Matthew-Garcia/SCARA-Robot/3D_Models/Ball Bearing 35x47x7mm.SLDPRT

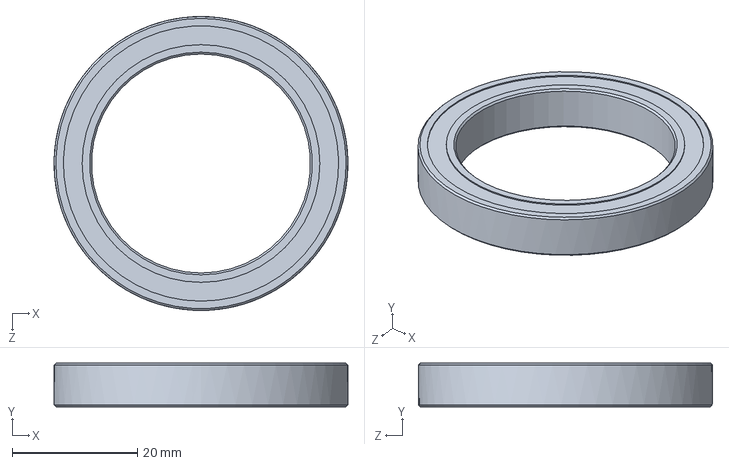
[picture p16: CAD file, 2025-07-01]
3D_Models/Ball Bearing 35x47x7mm.SLDPRT
47.0 x 7.00 x 47.0 mm
