Matthew-Garcia/SCARA-Robot/3D_Models/Arm 2 Cover.SLDPRT

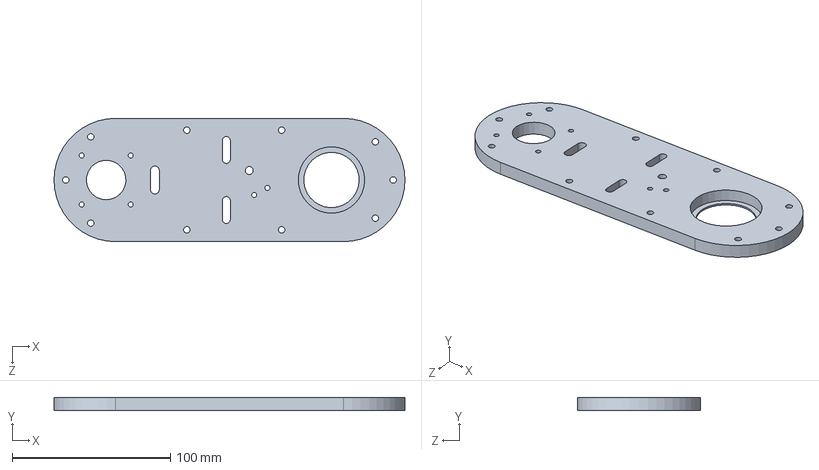
[picture p17: CAD file, 2025-07-01]
3D_Models/Arm 2 Cover.SLDPRT
222.0 x 8.00 x 78.0 mm
