Matthew-Garcia/SCARA-Robot/3D_Models/Z-axis Top Plate.SLDPRT

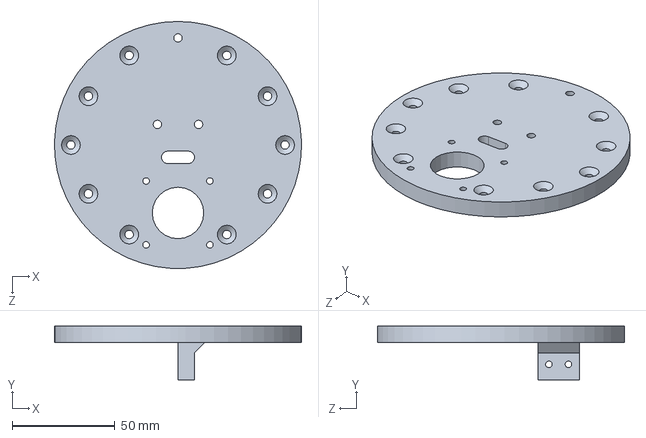
[picture p18: CAD file, 2025-07-01]
3D_Models/Z-axis Top Plate.SLDPRT
119.9 x 26.0 x 120.0 mm
