Matthew-Garcia/SCARA-Robot/3D_Models/Thrust Bearing - 40x60x13.SLDPRT

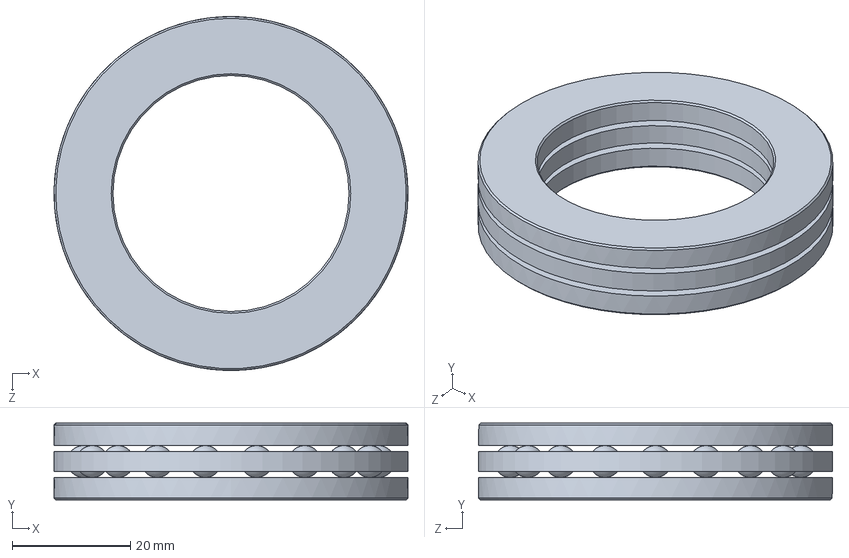
[picture p19: CAD file, 2025-07-01]
3D_Models/Thrust Bearing - 40x60x13.SLDPRT
60.0 x 13.0 x 60.0 mm
