Matthew-Garcia/SCARA-Robot/3D_Models/J3 Coupler.SLDPRT

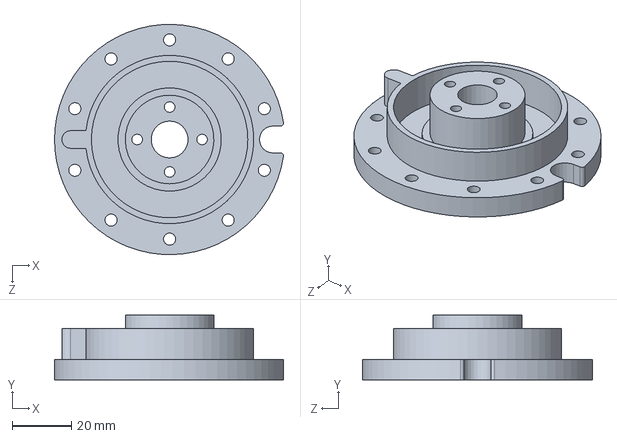
[picture p20: CAD file, 2025-07-01]
3D_Models/J3 Coupler.SLDPRT
77.6 x 22.0 x 78.0 mm
