Matthew-Garcia/SCARA-Robot/3D_Models/GT2 Belt 300mm 2.SLDPRT

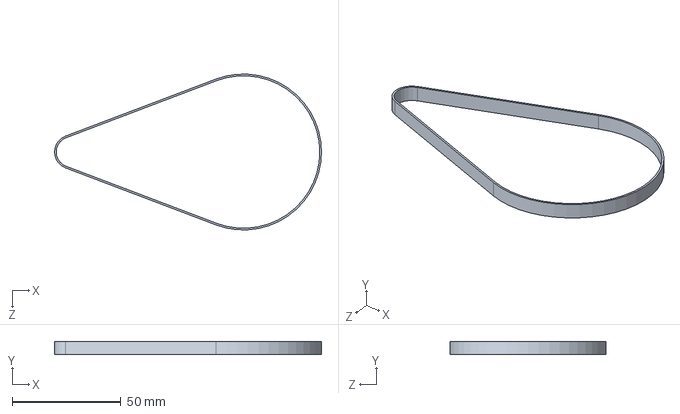
[picture p21: CAD file, 2025-07-01]
3D_Models/GT2 Belt 300mm 2.SLDPRT
122.6 x 6.00 x 71.5 mm
