Matthew-Garcia/SCARA-Robot/3D_Models/GT2 Belt 400mm.SLDPRT

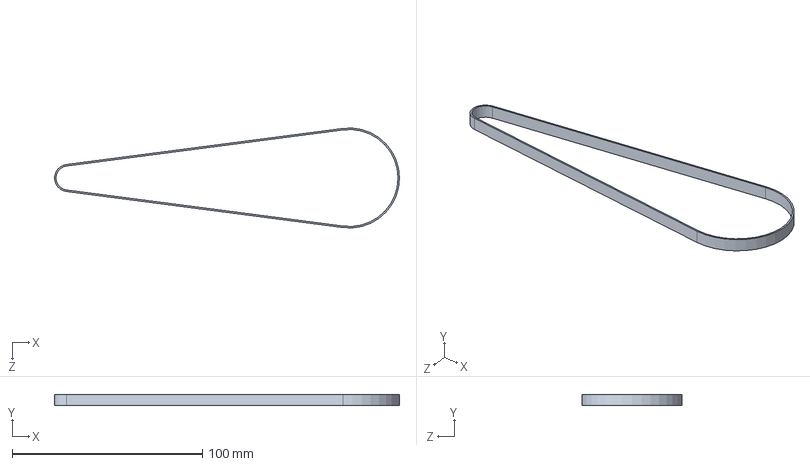
[picture p22: CAD file, 2025-07-01]
3D_Models/GT2 Belt 400mm.SLDPRT
181.4 x 6.00 x 52.5 mm
