Matthew-Garcia/SCARA-Robot/3D_Models/J1 coupler.SLDPRT

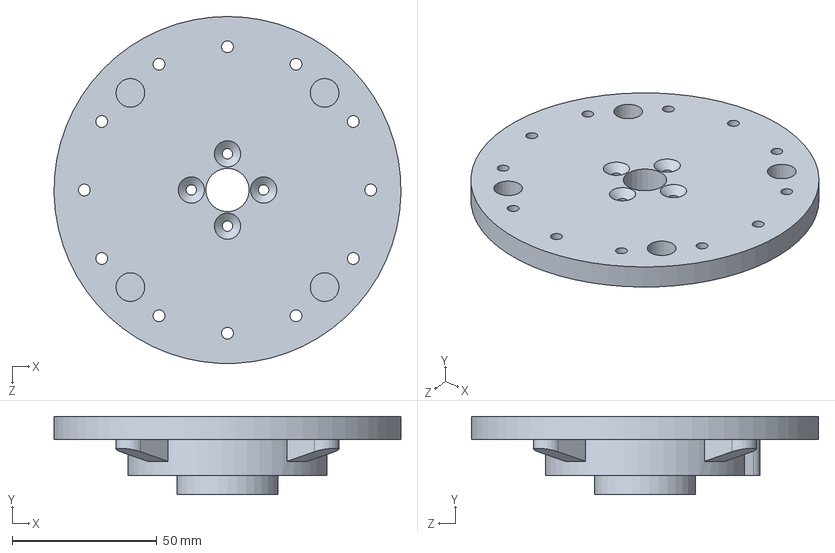
[picture p23: CAD file, 2025-07-01]
3D_Models/J1 coupler.SLDPRT
120.0 x 27.0 x 120.0 mm
