Matthew-Garcia/SCARA-Robot/3D_Models/Arm 2.SLDPRT

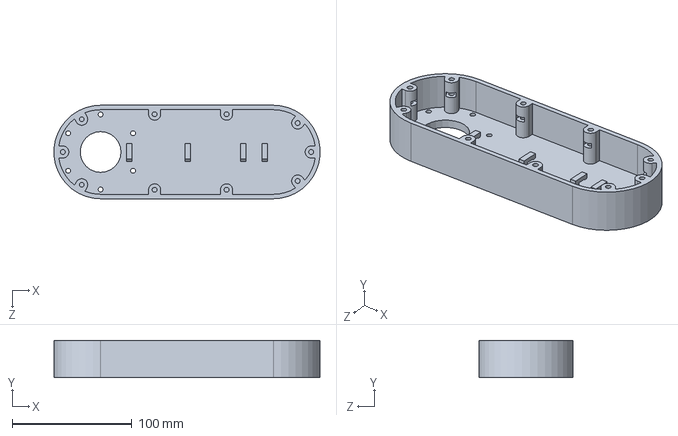
[picture p24: CAD file, 2025-07-01]
3D_Models/Arm 2.SLDPRT
221.7 x 31.0 x 78.0 mm
