Matthew-Garcia/SCARA-Robot/3D_Models/Gripper Mechanism Slider.SLDPRT

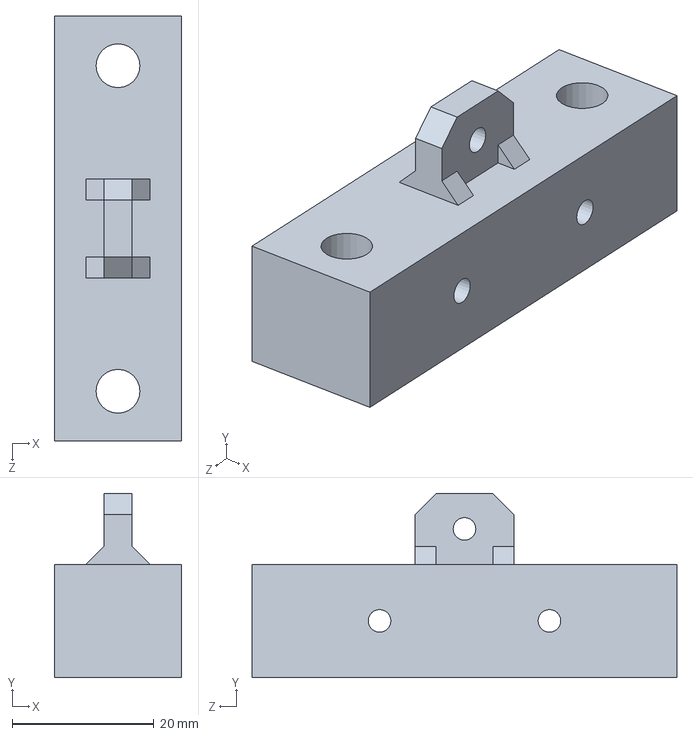
[picture p25: CAD file, 2025-07-01]
3D_Models/Gripper Mechanism Slider.SLDPRT
18.0 x 26.0 x 60.0 mm
