Matthew-Garcia/SCARA-Robot/3D_Models/Arduino UNO case p1.SLDPRT

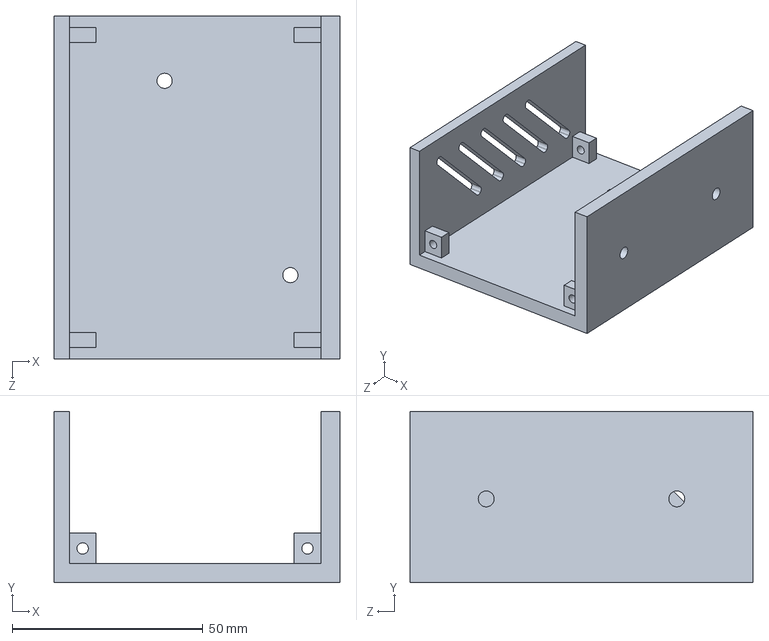
[picture p26: CAD file, 2025-07-01]
3D_Models/Arduino UNO case p1.SLDPRT
75.0 x 45.0 x 90.0 mm
