Matthew-Garcia/SCARA-Robot/3D_Models/Gripper End.SLDPRT

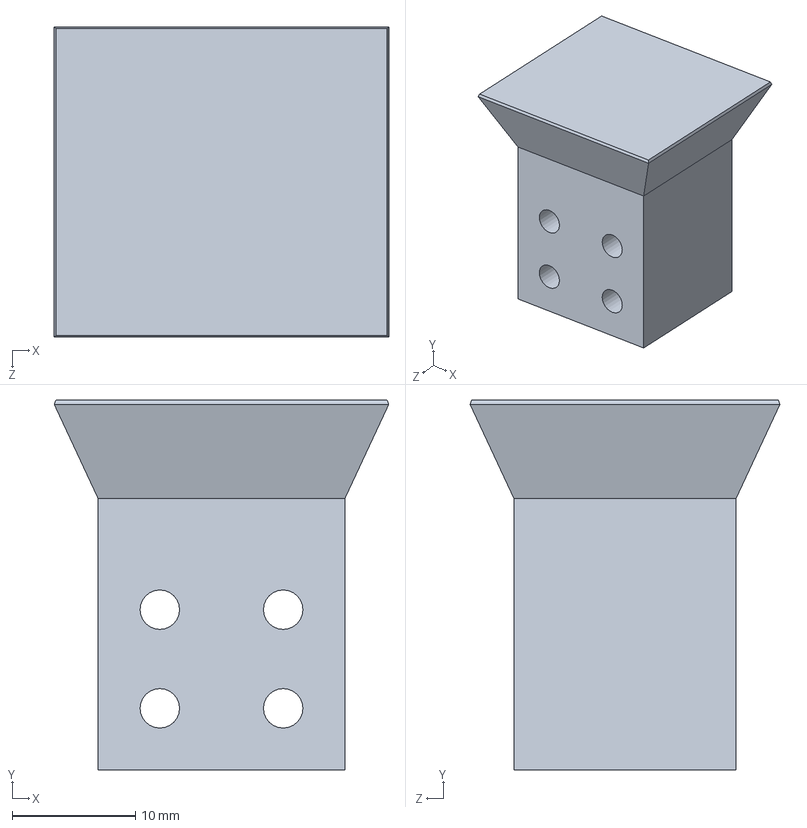
[picture p27: CAD file, 2025-07-01]
3D_Models/Gripper End.SLDPRT
27.1 x 30.0 x 25.1 mm
