Matthew-Garcia/SCARA-Robot/3D_Models/GT2 Pulley - 90 teeth - J3.SLDPRT

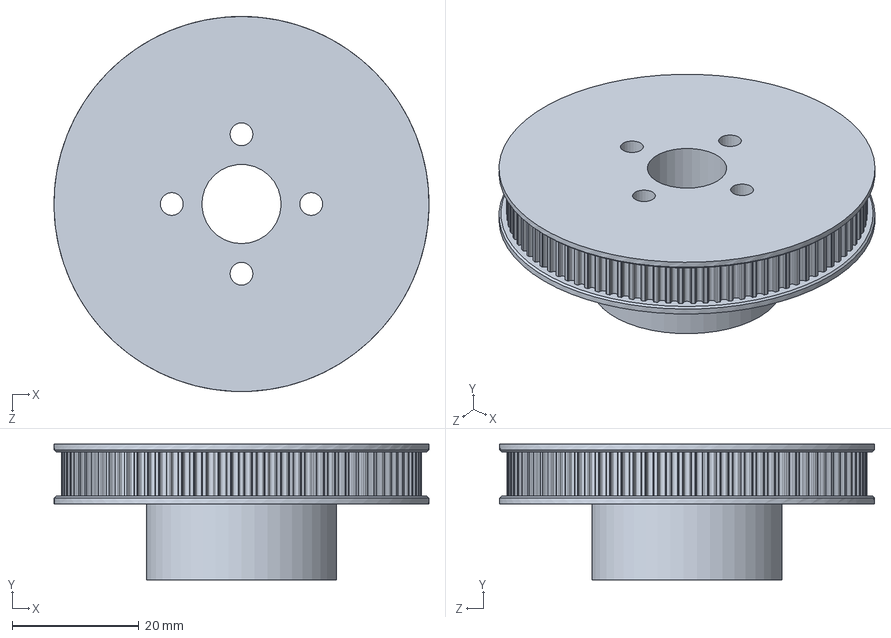
[picture p28: CAD file, 2025-07-01]
3D_Models/GT2 Pulley - 90 teeth - J3.SLDPRT
59.2 x 21.4 x 59.2 mm
