Matthew-Garcia/SCARA-Robot/3D_Models/Top cover.SLDPRT

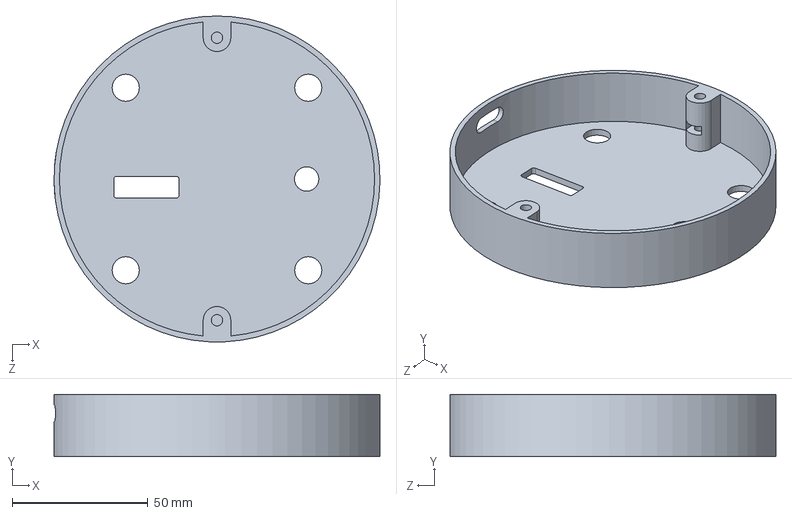
[picture p29: CAD file, 2025-07-01]
3D_Models/Top cover.SLDPRT
120.0 x 23.0 x 120.0 mm
