Matthew-Garcia/SCARA-Robot/3D_Models/Servo MG996R Horn.step

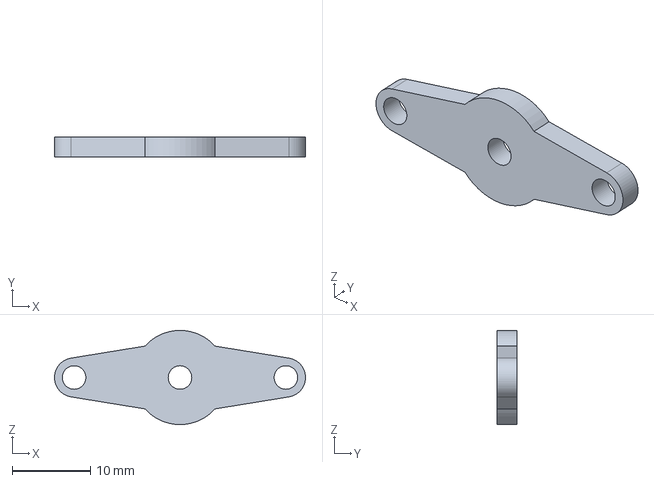
[picture p30: CAD file, 2025-07-01]
3D_Models/Servo MG996R Horn.step
32.0 x 2.50 x 12.0 mm
