Matthew-Garcia/SCARA-Robot/3D_Models/Base cover.SLDPRT

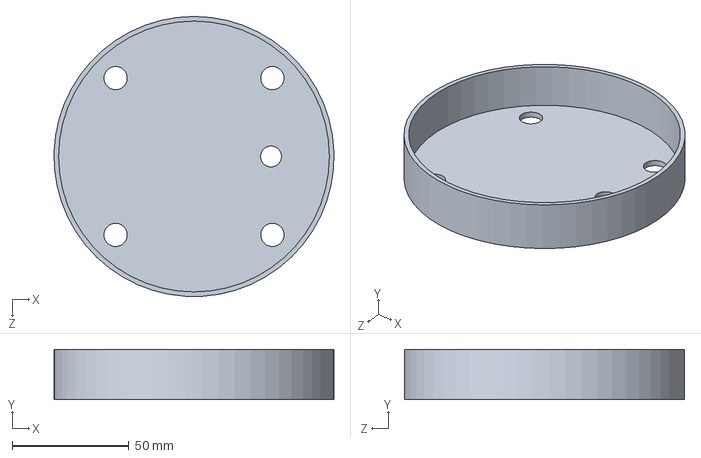
[picture p31: CAD file, 2025-07-01]
3D_Models/Base cover.SLDPRT
119.9 x 21.5 x 120.0 mm
