Matthew-Garcia/SCARA-Robot/3D_Models/Servo Motor MG996R 3D Model.step

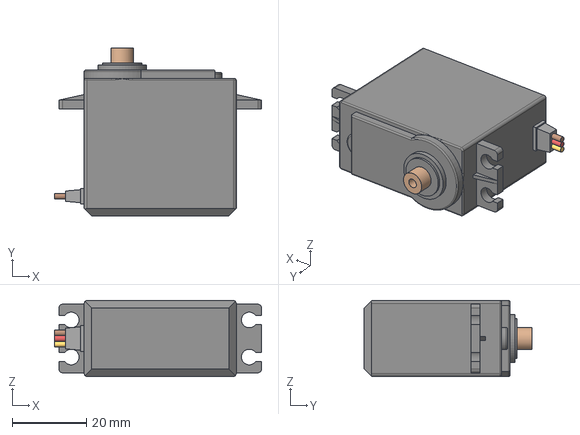
[picture p32: CAD file, 2025-07-01]
3D_Models/Servo Motor MG996R 3D Model.step
55.8 x 45.2 x 20.5 mm
