Matthew-Garcia/SCARA-Robot/3D_Models/Z-axis Bottom Plate.SLDPRT

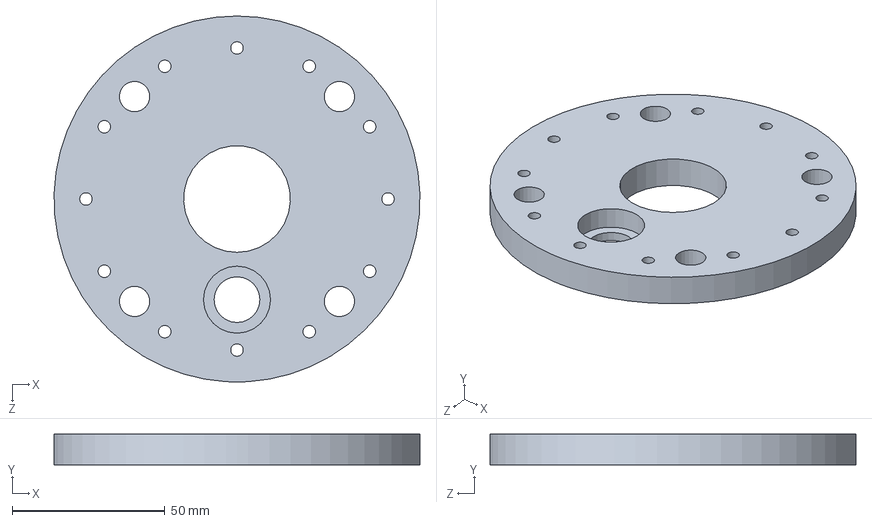
[picture p33: CAD file, 2025-07-01]
3D_Models/Z-axis Bottom Plate.SLDPRT
119.9 x 10.0 x 120.0 mm
