Matthew-Garcia/SCARA-Robot/3D_Models/NEMA 17 Stepper L24mm - 20mm shaft.step

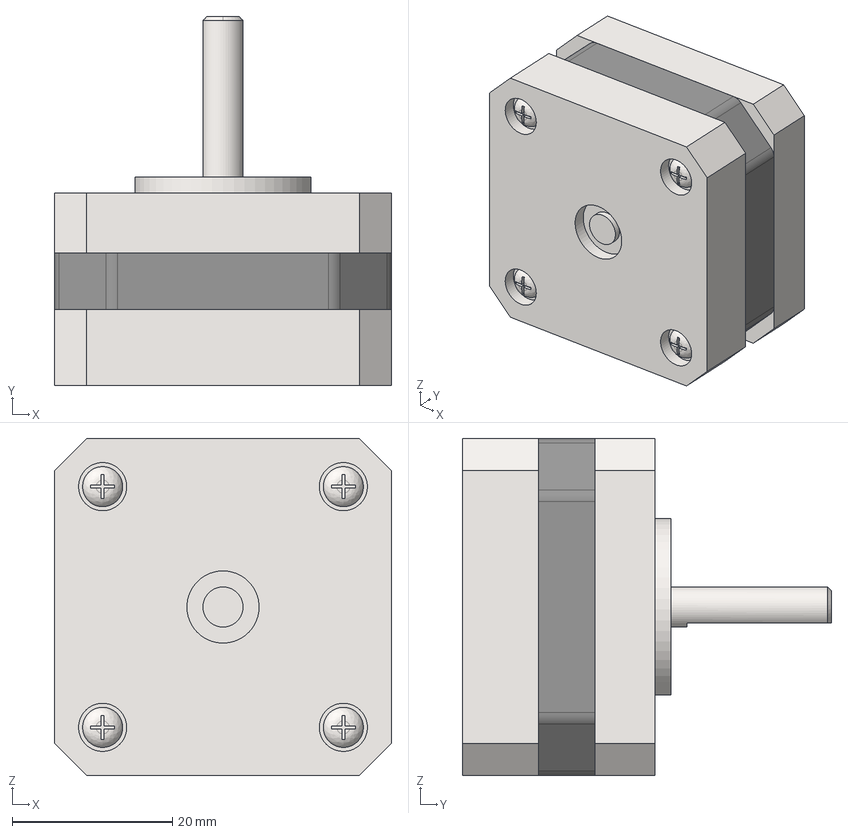
[picture p34: CAD file, 2025-07-01]
3D_Models/NEMA 17 Stepper L24mm - 20mm shaft.step
42.0 x 46.0 x 42.0 mm
