Matthew-Garcia/SCARA-Robot/3D_Models/Base.SLDPRT

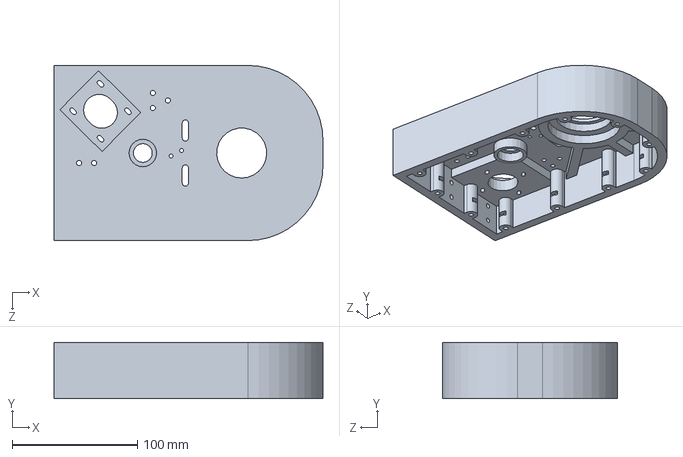
[picture p35: CAD file, 2025-07-01]
3D_Models/Base.SLDPRT
215.0 x 45.0 x 140.0 mm
