Matthew-Garcia/SCARA-Robot/3D_Models/GT2 Pulley - 92 teeth - J2.SLDPRT

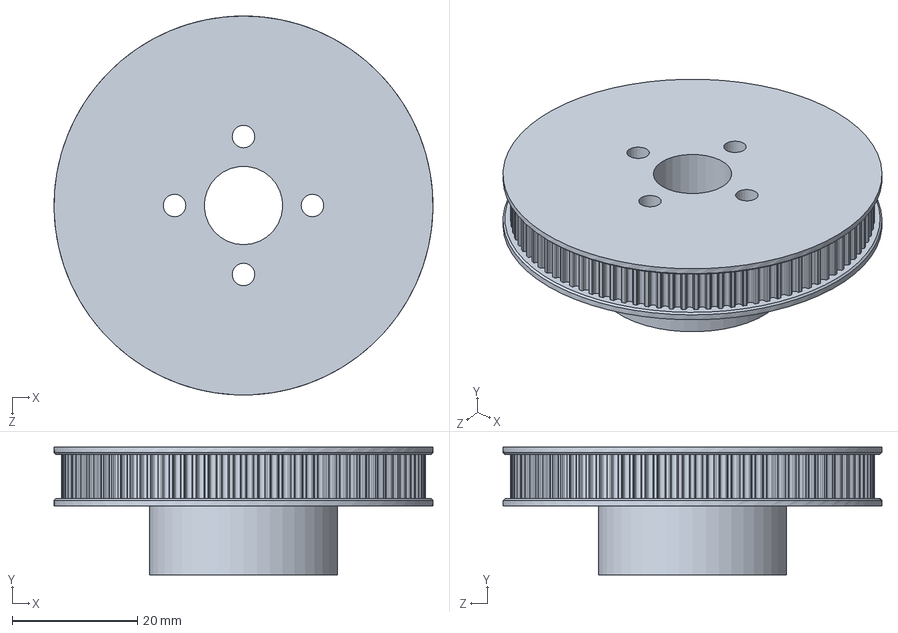
[picture p36: CAD file, 2025-07-01]
3D_Models/GT2 Pulley - 92 teeth - J2.SLDPRT
60.4 x 20.4 x 60.5 mm
