Matthew-Garcia/SCARA-Robot/3D_Models/Ball Bearing 608 - 8x22x7mm.SLDPRT

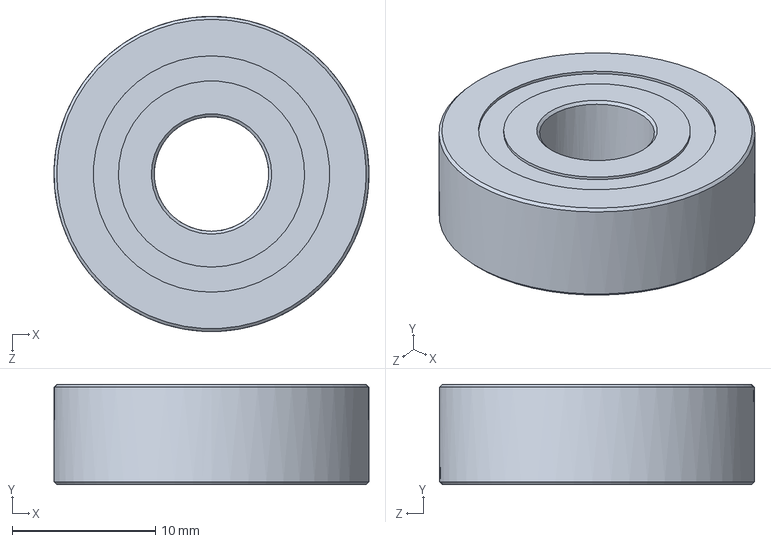
[picture p37: CAD file, 2025-07-01]
3D_Models/Ball Bearing 608 - 8x22x7mm.SLDPRT
22.0 x 7.00 x 22.0 mm
