Matthew-Garcia/SCARA-Robot/3D_Models/GT2 Belt 200mm.SLDPRT

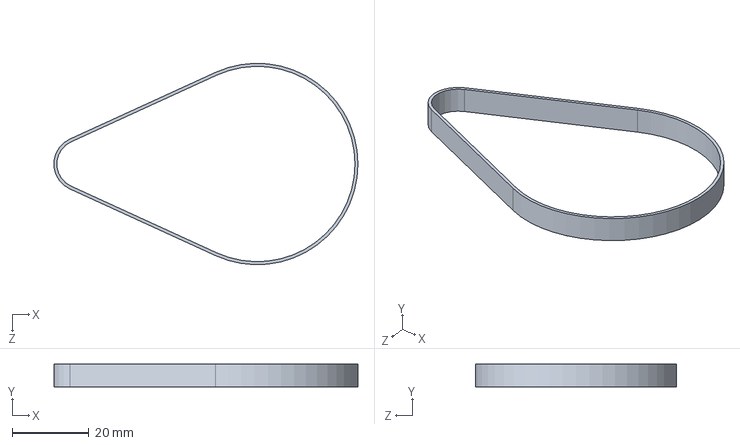
[picture p38: CAD file, 2025-07-01]
3D_Models/GT2 Belt 200mm.SLDPRT
79.4 x 6.00 x 52.6 mm
