Matthew-Garcia/SCARA-Robot/3D_Models/Smooth Rod Clamp.SLDPRT

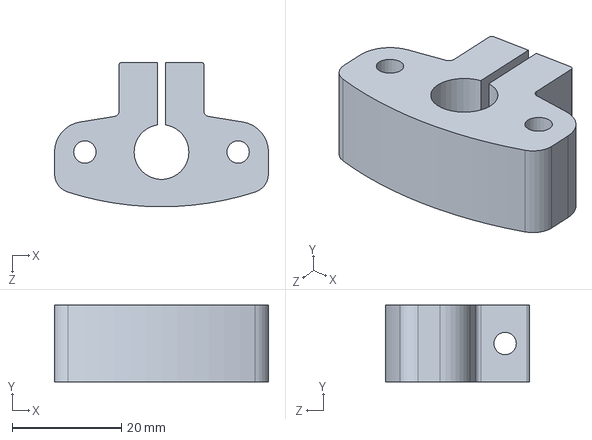
[picture p39: CAD file, 2025-07-01]
3D_Models/Smooth Rod Clamp.SLDPRT
39.1 x 14.0 x 26.4 mm
