Matthew-Garcia/SCARA-Robot/3D_Models/J2 Coupler.SLDPRT

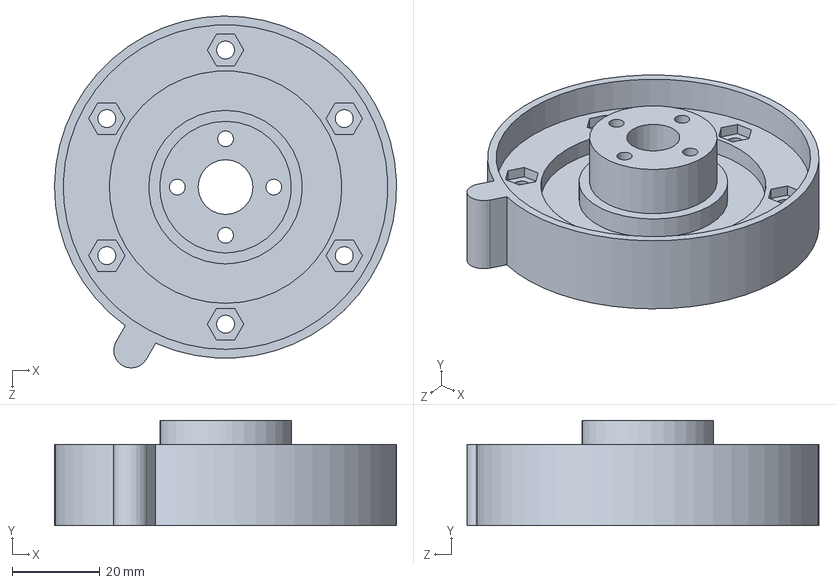
[picture p40: CAD file, 2025-07-01]
3D_Models/J2 Coupler.SLDPRT
78.0 x 24.0 x 80.2 mm
