Matthew-Garcia/SCARA-Robot/3D_Models/Smooth Rod D10mm L400mm.SLDPRT

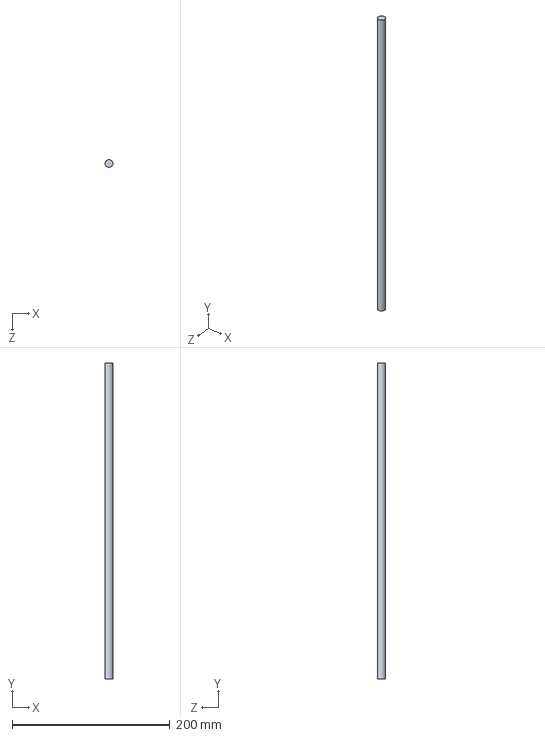
[picture p41: CAD file, 2025-07-01]
3D_Models/Smooth Rod D10mm L400mm.SLDPRT
10.0 x 400.0 x 10.0 mm
