Matthew-Garcia/SCARA-Robot/3D_Models/Z-axis Mount Platform.SLDPRT

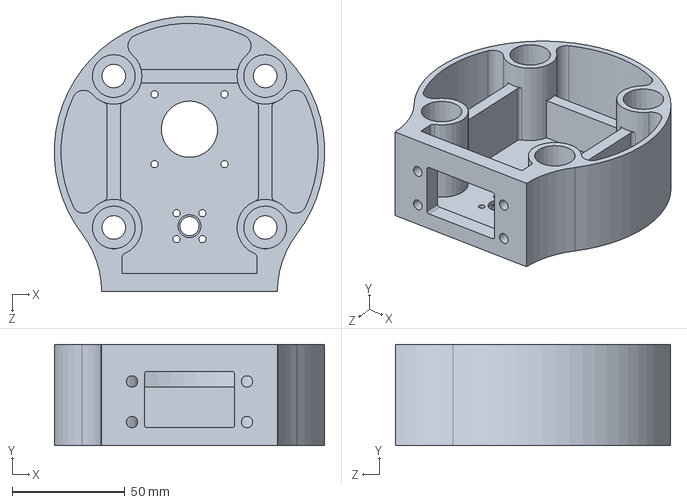
[picture p42: CAD file, 2025-07-01]
3D_Models/Z-axis Mount Platform.SLDPRT
119.9 x 45.0 x 122.0 mm
