Matthew-Garcia/SCARA-Robot/3D_Models/Thrust Bearing 35x52x12mm.SLDPRT

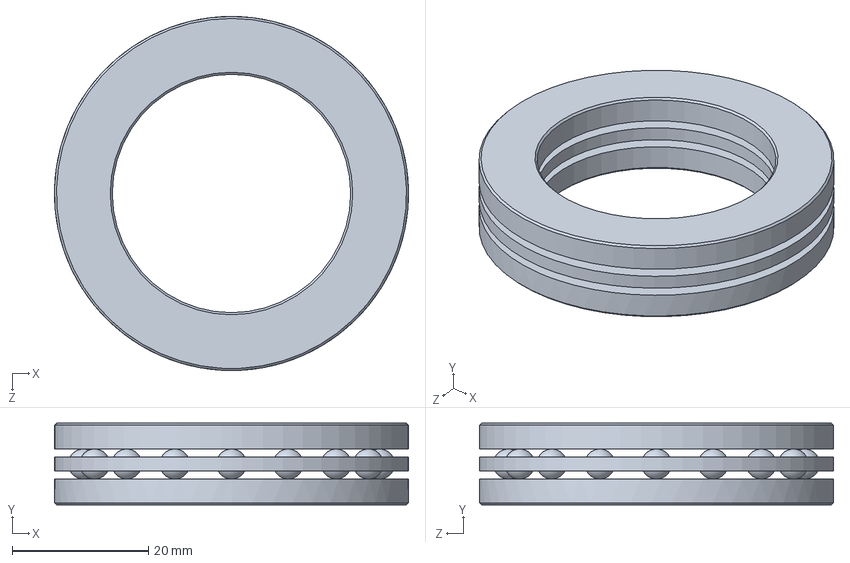
[picture p43: CAD file, 2025-07-01]
3D_Models/Thrust Bearing 35x52x12mm.SLDPRT
52.0 x 12.0 x 52.0 mm
