Matthew-Garcia/SCARA-Robot/3D_Models/Gripper Cover.SLDPRT

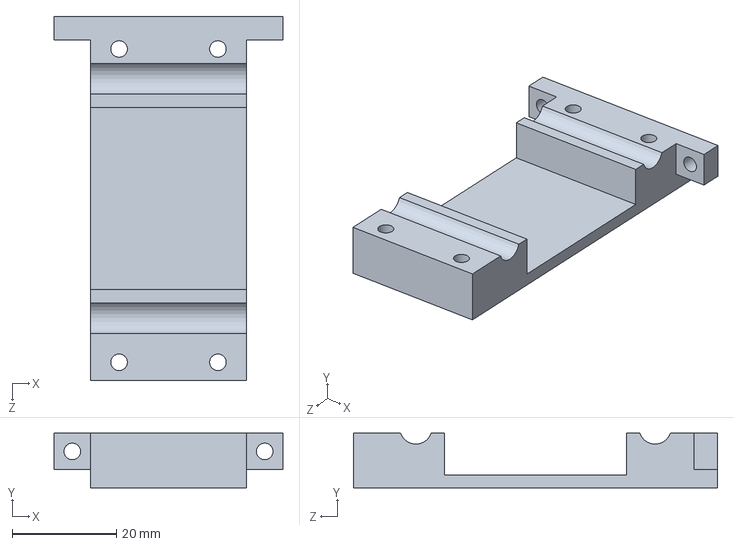
[picture p44: CAD file, 2025-07-01]
3D_Models/Gripper Cover.SLDPRT
44.0 x 10.5 x 70.0 mm
