Matthew-Garcia/SCARA-Robot/3D_Models/Gripper link 1.SLDPRT

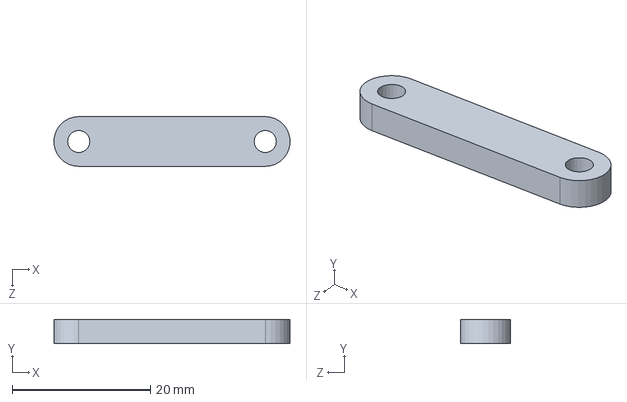
[picture p45: CAD file, 2025-07-01]
3D_Models/Gripper link 1.SLDPRT
34.2 x 3.50 x 7.20 mm
