Matthew-Garcia/SCARA-Robot/3D_Models/Gripper to J3 connector.SLDPRT

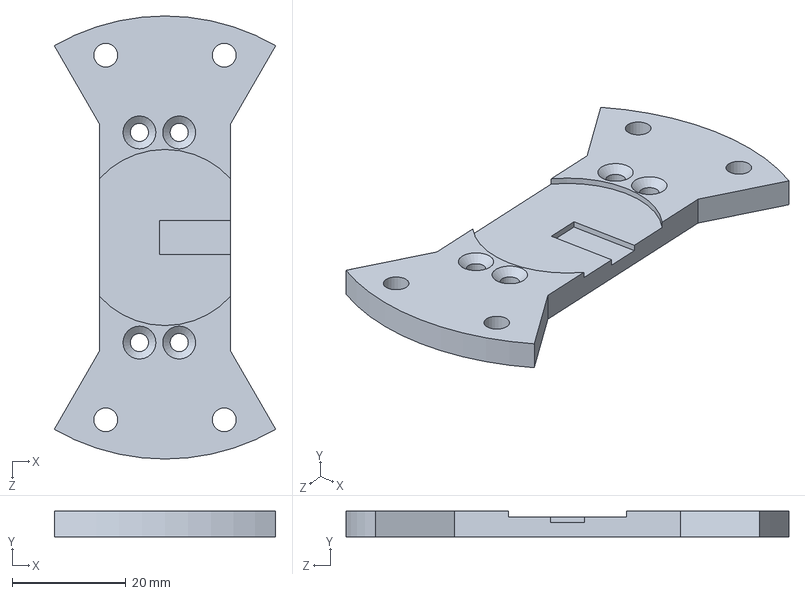
[picture p46: CAD file, 2025-07-01]
3D_Models/Gripper to J3 connector.SLDPRT
39.0 x 4.50 x 78.0 mm
