Matthew-Garcia/SCARA-Robot/3D_Models/Micro switch.step

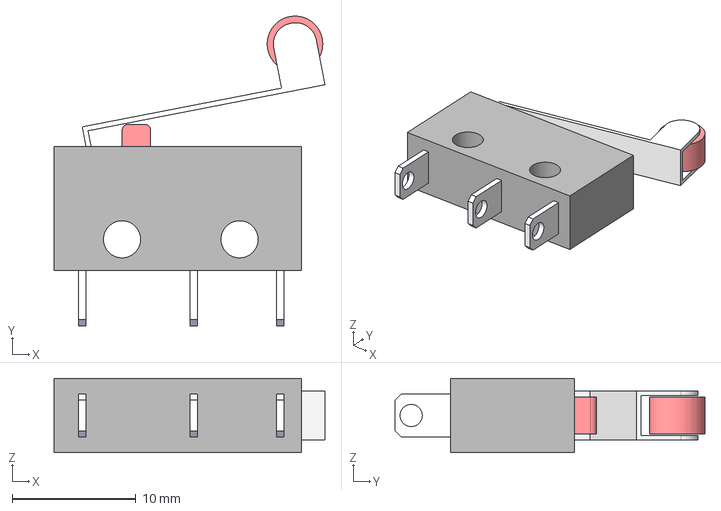
[picture p47: CAD file, 2025-07-01]
3D_Models/Micro switch.step
21.9 x 25.0 x 6.00 mm
