Matthew-Garcia/SCARA-Robot/3D_Models/Ball Bearing 30x42x7mm.SLDPRT

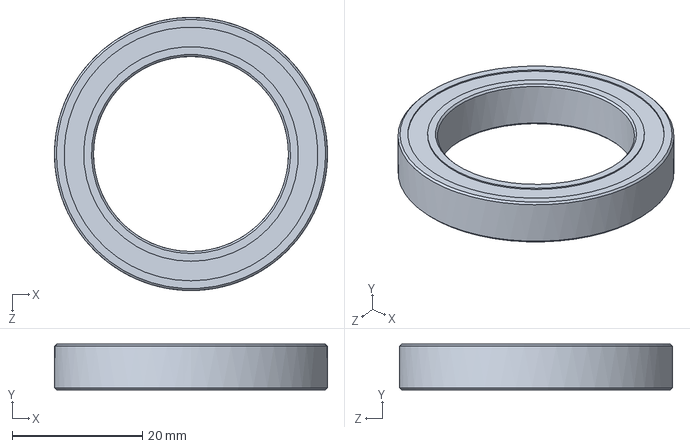
[picture p48: CAD file, 2025-07-01]
3D_Models/Ball Bearing 30x42x7mm.SLDPRT
42.0 x 7.00 x 42.0 mm
