Matthew-Garcia/SCARA-Robot/3D_Models/Gripper link 2.SLDPRT

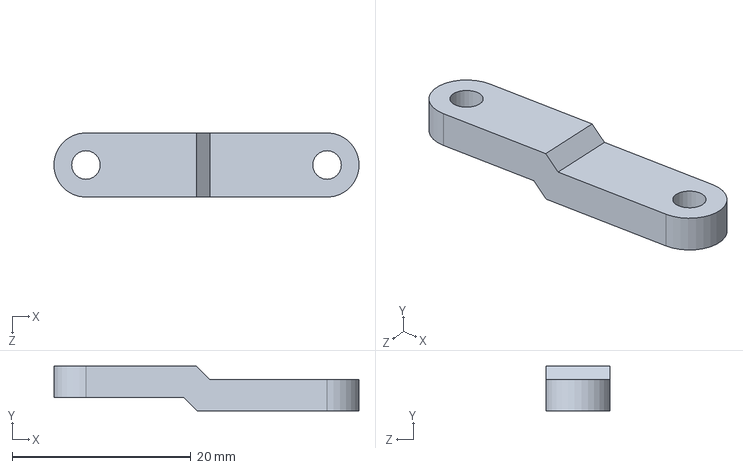
[picture p49: CAD file, 2025-07-01]
3D_Models/Gripper link 2.SLDPRT
34.2 x 5.00 x 7.20 mm
