Matthew-Garcia/SCARA-Robot/3D_Models/Stepper NEMA 17 -  20mm shaft.step

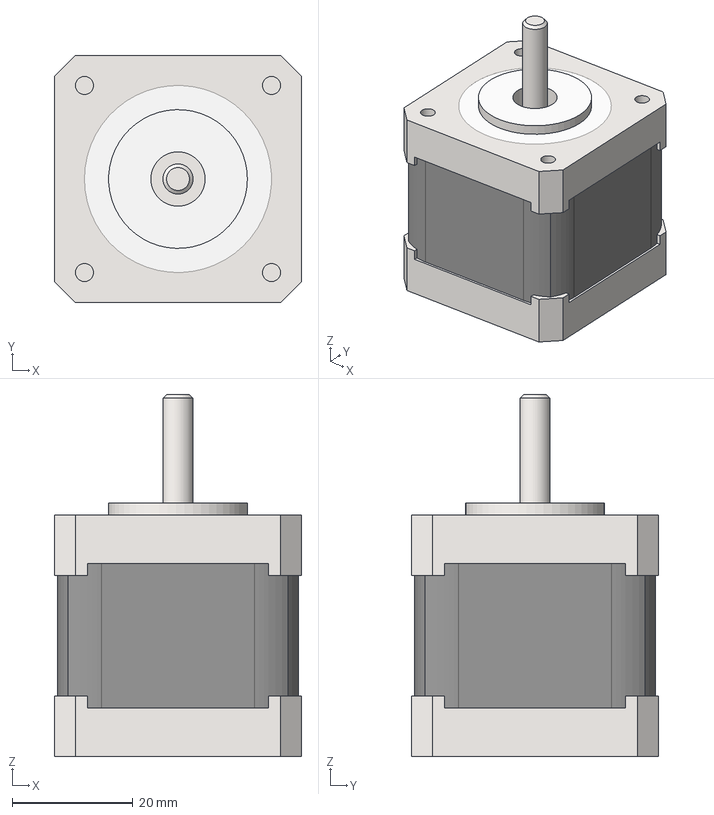
[picture p50: CAD file, 2025-07-01]
3D_Models/Stepper NEMA 17 - 20mm shaft.step
41.0 x 41.0 x 60.0 mm
